Anyboard/anyboard/anypawn_p2-alpha/firmware/anypawn-rfduino/protocol.h

#ifndef PROTOCOL_h
#define PROTOCOL_h

// TOKEN FIRMWARE METADATA
#define NAME    "AnyBoard Pawn"
#define VERSION "0.1"
#define UUID    "3191-6275-32g4"


// Status commands
const uint8_t GET_NAME             = 32;
const uint8_t GET_VERSION          = 33;
const uint8_t GET_UUID             = 34;
const uint8_t HAS_LED              = 64;
const uint8_t HAS_LED_COLOR        = 65;
const uint8_t HAS_VIBRATION        = 66;
const uint8_t HAS_COLOR_DETECTION  = 67;
const uint8_t HAS_LED_SCREEN       = 68;
const uint8_t HAS_RFID             = 71;
const uint8_t HAS_NFC              = 72;
const uint8_t HAS_ACCELEROMETER    = 73;
const uint8_t HAS_TEMPERATURE      = 74;
const uint8_t READ_COLOR           = 136;

//Token-solo events
const uint8_t TAP				           = 201; //C9
const uint8_t DOUBLE_TAP		       = 202; //CA
const uint8_t SHAKE				         = 203; //CB
const uint8_t TILT                 = 204; //CC
const uint8_t TRIG_ROT             = 220;
const uint8_t A_TRIG_ROT           = 221;

//Token-constraint events
const uint8_t MOVE                 = 194; //C2 (+ 2nd and 3rd bytes for current and last sector)

//Token-token events
//TBD

//feedbacks
const uint8_t COUNT                = 205; //CD
const uint8_t DISPLAY_X            = 206; //CE
const uint8_t VIBRATE              = 200; //C8
const uint8_t DISPLAY_DIGIT		     = 207;
const uint8_t DISPLAY_W		   	     = 208;
const uint8_t DISPLAY_UP		       = 209;
const uint8_t DISPLAY_DOWN		     = 210;

const uint8_t LED_OFF2             = 128;
const uint8_t LED_ON2              = 129;
const uint8_t LED_BLINK            = 130;


#endif
